Heather-Wimberley/eee3088f-group5-stm32HAT/Firmware/Core/Src/Sensors/inc/prox.h

/*
 * prox.h
 *
 *  Created on: May 6, 2022
 *      Author: kelvi
 */

#ifndef SRC_SENSORS_VL6180API_PROX_H_
#define SRC_SENSORS_VL6180API_PROX_H_
#include "vl6180_api.h"
#include "stm32f0xx_hal.h"
#include "types.h"


#define PROX_I2C_ADDRESS 0x29

extern VL6180Dev_t vl6180Handler;


SensorErrorType ProximitySensor_Start(I2C_HandleTypeDef* i2cHandler);

SensorErrorType ProximitySensor_Stop(void);
SensorErrorType ProximitySensor_IsReady(void);
SensorErrorType ProximitySensor_GetSingleShotMeasurement(int32_t* result);

SensorErrorType ProximitySensor_OnInterruptStarted(void);
SensorErrorType ProximitySensor_Start_IT(I2C_HandleTypeDef* i2cHandler, int freq);
SensorErrorType ProximitySensor_OnInterruptStarted(void);
SensorErrorType ProximitySensor_OnInterruptDetected(int32_t* result);


#endif /* SRC_SENSORS_VL6180API_PROX_H_ */
